purduerov/X17-Pi-Shield/3D_MODELS/ISOW1432BDFMR.step

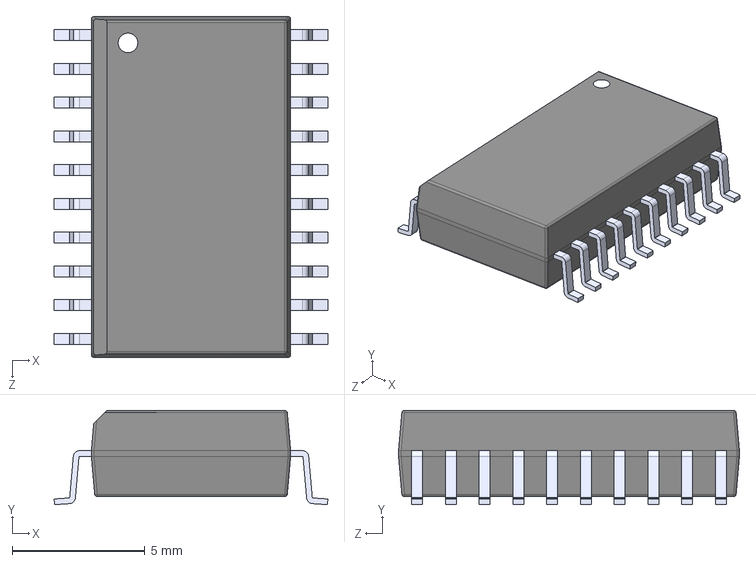
[picture p18: CAD file, 2024-11-07]
3D_MODELS/ISOW1432BDFMR.step
10.3 x 3.55 x 12.8 mm
