purduerov/X17-Pi-Shield/3D_MODELS/INA260AIPW.step

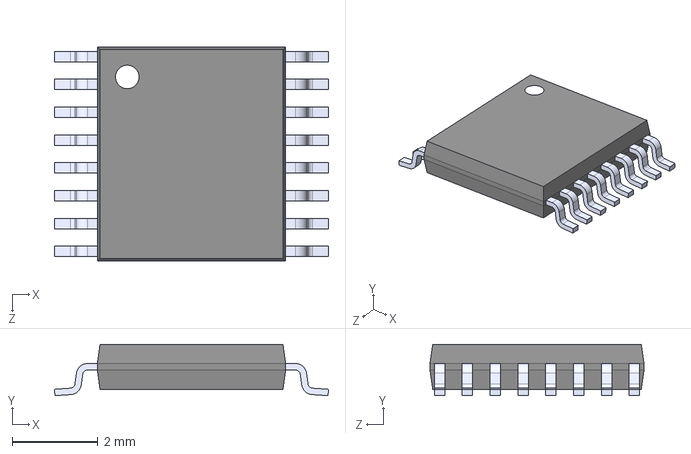
[picture p19: CAD file, 2024-10-12]
3D_MODELS/INA260AIPW.step
6.40 x 1.20 x 5.00 mm
