purduerov/X17-Pi-Shield/3D_MODELS/430450212.stp

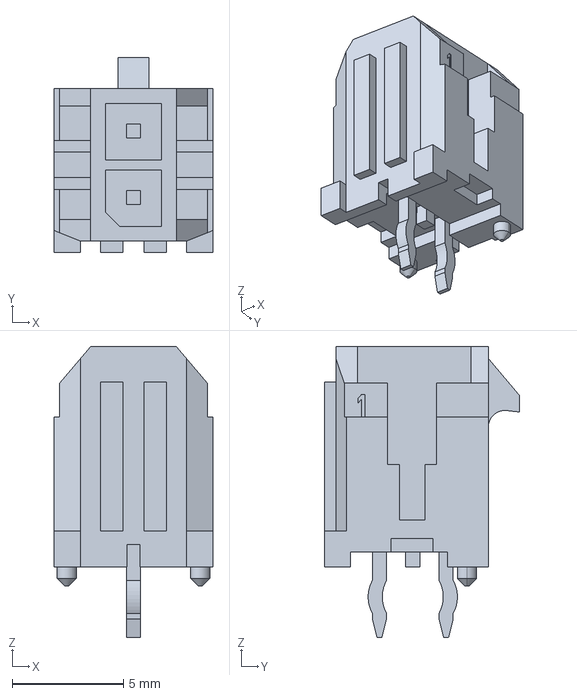
[picture p20: CAD file, 2024-11-07]
3D_MODELS/430450212.stp
7.15 x 8.77 x 13.1 mm
