purduerov/X17-Pi-Shield/3D_MODELS/430450612.stp

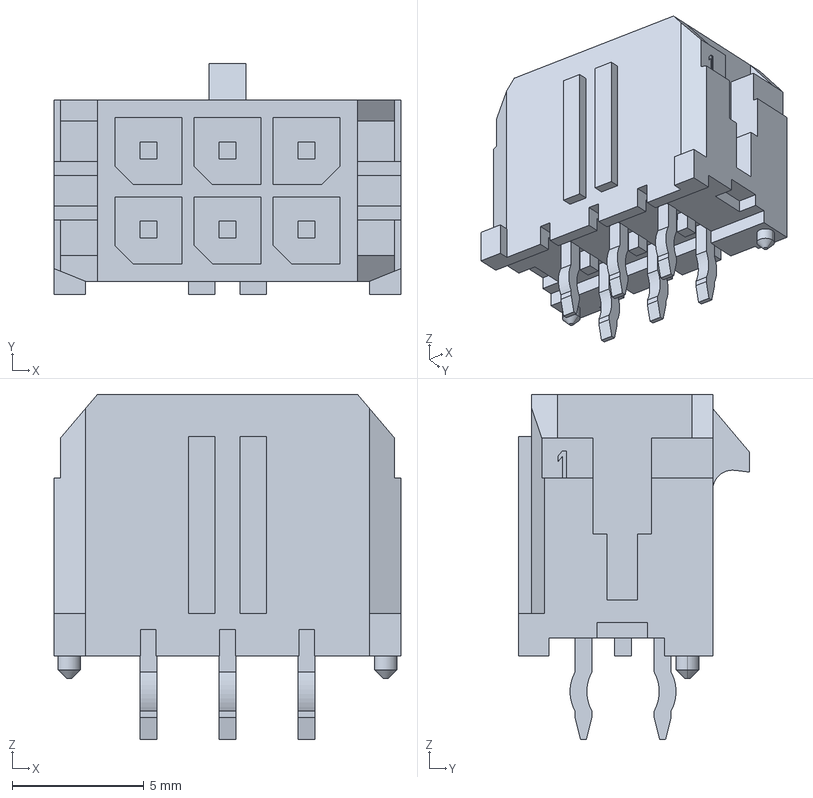
[picture p21: CAD file, 2024-11-07]
3D_MODELS/430450612.stp
13.2 x 8.77 x 13.1 mm
